yasunoxx/Z80proto/sch/Z80proto2/SPI40x4LCD.kicad_sch

## KiCad design sch/Z80proto2/SPI40x4LCD.kicad_sch (2025-04-16)

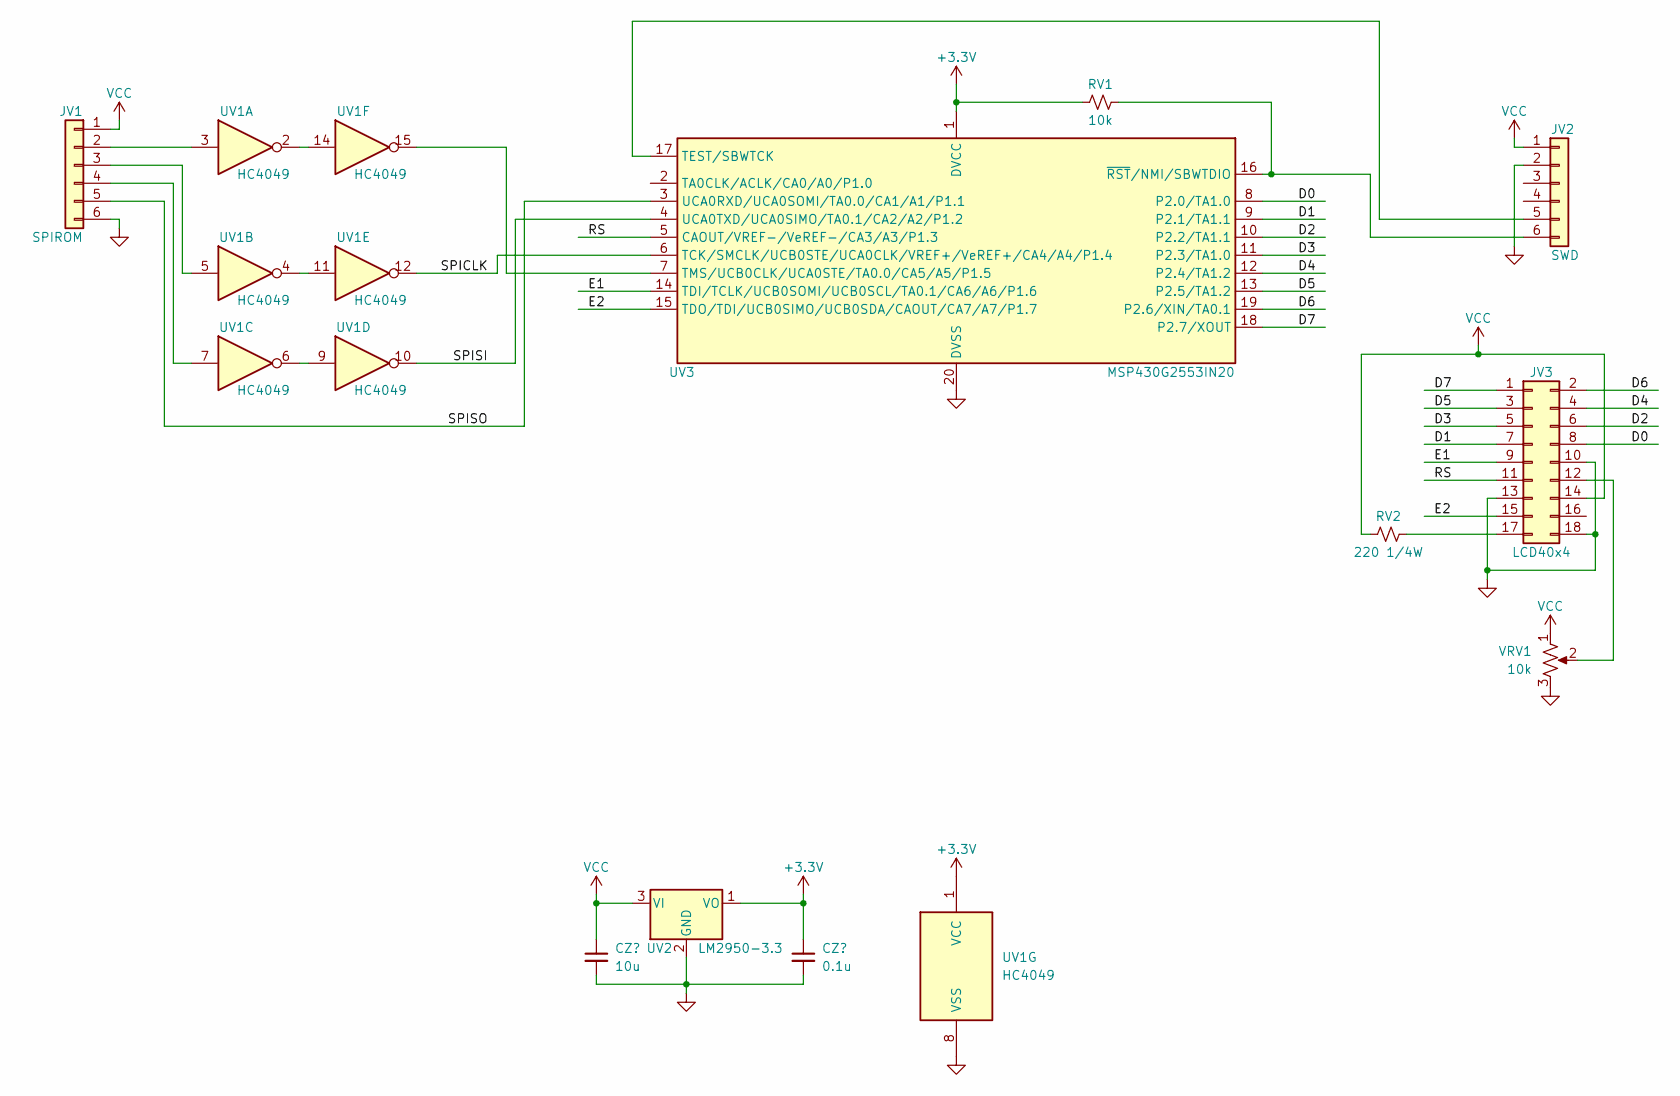
[picture p12: schematic SPI40x4LCD.kicad_sch]

Parts:
JV1: SPIROM
JV2: SWD
JV3: LCD40x4
RV1: 10k
RV2: 220 1/4W
UV1: HC4049
UV2: LM2950-3.3; TO-92_Inline
UV3: MSP430G2553IN20; DIP-20_W7.62mm
VRV1: 10k

Connections:
D0: JV3.8, UV3.8 (P2.0/TA1.0)
D1: JV3.7, UV3.9 (P2.1/TA1.1)
D2: JV3.6, UV3.10 (P2.2/TA1.1)
D3: JV3.5, UV3.11 (P2.3/TA1.0)
D4: JV3.4, UV3.12 (P2.4/TA1.2)
D5: JV3.3, UV3.13 (P2.5/TA1.2)
D6: JV3.2, UV3.19 (P2.6/XIN/TA0.1)
D7: JV3.1, UV3.18 (P2.7/XOUT)
E1: JV3.9, UV3.14 (TDI/TCLK/UCB0SOMI/UCB0SCL/TA0.1/CA6/A6/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)
E2: JV3.15, UV3.15 (TDO/TDI/UCB0SIMO/UCB0SDA/CAOUT/CA7/A7/P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)
unnamed: JV1.2, UV1.3
unnamed: JV1.3, UV1.5
unnamed: JV1.4, UV1.7
unnamed: JV2.5, UV3.17 (TEST/SBWTCK)
unnamed: JV2.6, RV1.2, UV3.16 (~RST/NMI/SBWTDIO)
unnamed: JV3.10, JV3.13, JV3.18
unnamed: JV3.12, VRV1.2
unnamed: JV3.14, RV2.1
unnamed: JV3.17, RV2.2
unnamed: RV1.1, UV3.1 (DVCC)
unnamed: UV1.6, UV1.9
unnamed: UV1.4, UV1.11
unnamed: UV1.2, UV1.14
unnamed: UV1.15, UV3.7 (TMS/UCB0CLK/UCA0STE/TA0.0/CA5/A5/P1.5)
RS: JV3.11, UV3.5 (CAOUT/VREF-/VeREF-/CA3/A3/P1.3)
SPICLK: UV1.12, UV3.6 (TCK/SMCLK/UCB0STE/UCA0CLK/VREF+/VeREF+/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)
SPISI: UV1.10, UV3.4 (UCA0TXD/UCA0SIMO/TA0.1/CA2/A2/P1.2)
SPISO: JV1.5, UV3.3 (UCA0RXD/UCA0SOMI/TA0.0/CA1/A1/P1.1)
