yasunoxx/Z80proto/sch/Z80proto-SAKI80/Comm_Module.kicad_sch

## KiCad design sch/Z80proto-SAKI80/Comm_Module.kicad_sch (2025-09-18, an earlier design)

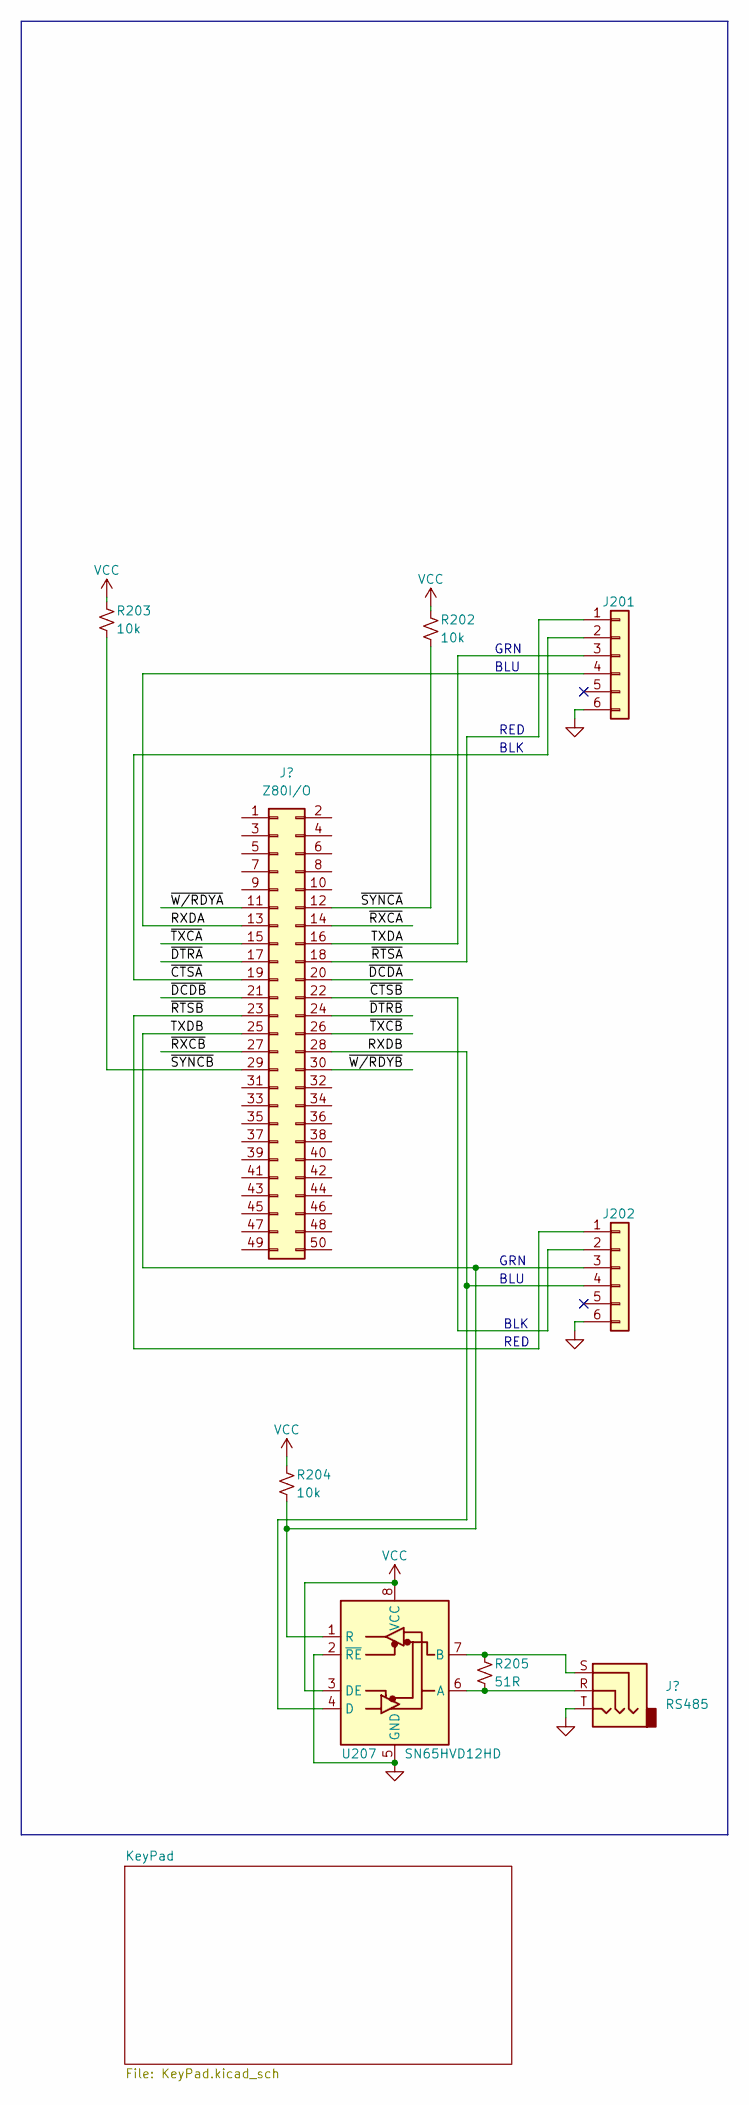
[picture p16: schematic Comm_Module.kicad_sch]

Parts:
J201, J202: Conn_01x06
R202, R203, R204: 10k
R205: 51R
U207: SN65HVD12HD; SOIC-8_3.9x4.9mm_P1.27mm

Connections:
unnamed: R205.1, U207.7 (B)
unnamed: R205.2, U207.6 (A)
unnamed: U207.2 (~RE), U207.5 (GND)
unnamed: U207.3 (DE), U207.8 (VCC)
RXDA: J201.4
RXDB: J202.4, U207.4 (D)
TXDA: J201.3
TXDB: J202.3, R204.2, U207.1 (R)
~CTSA: J201.2
~CTSB: J202.2
~RTSA: J201.1
~RTSB: J202.1
~SYNCA: R202.2
~SYNCB: R203.2

Notes on the sheet:
BLK
RED
BLU
GRN
