yasunoxx/Z80proto/sch/Z80proto-SAKI80/Z80proto-SAKI80.kicad_sch

## KiCad design sch/Z80proto-SAKI80/Z80proto-SAKI80.kicad_sch (2025-07-02, an earlier design)

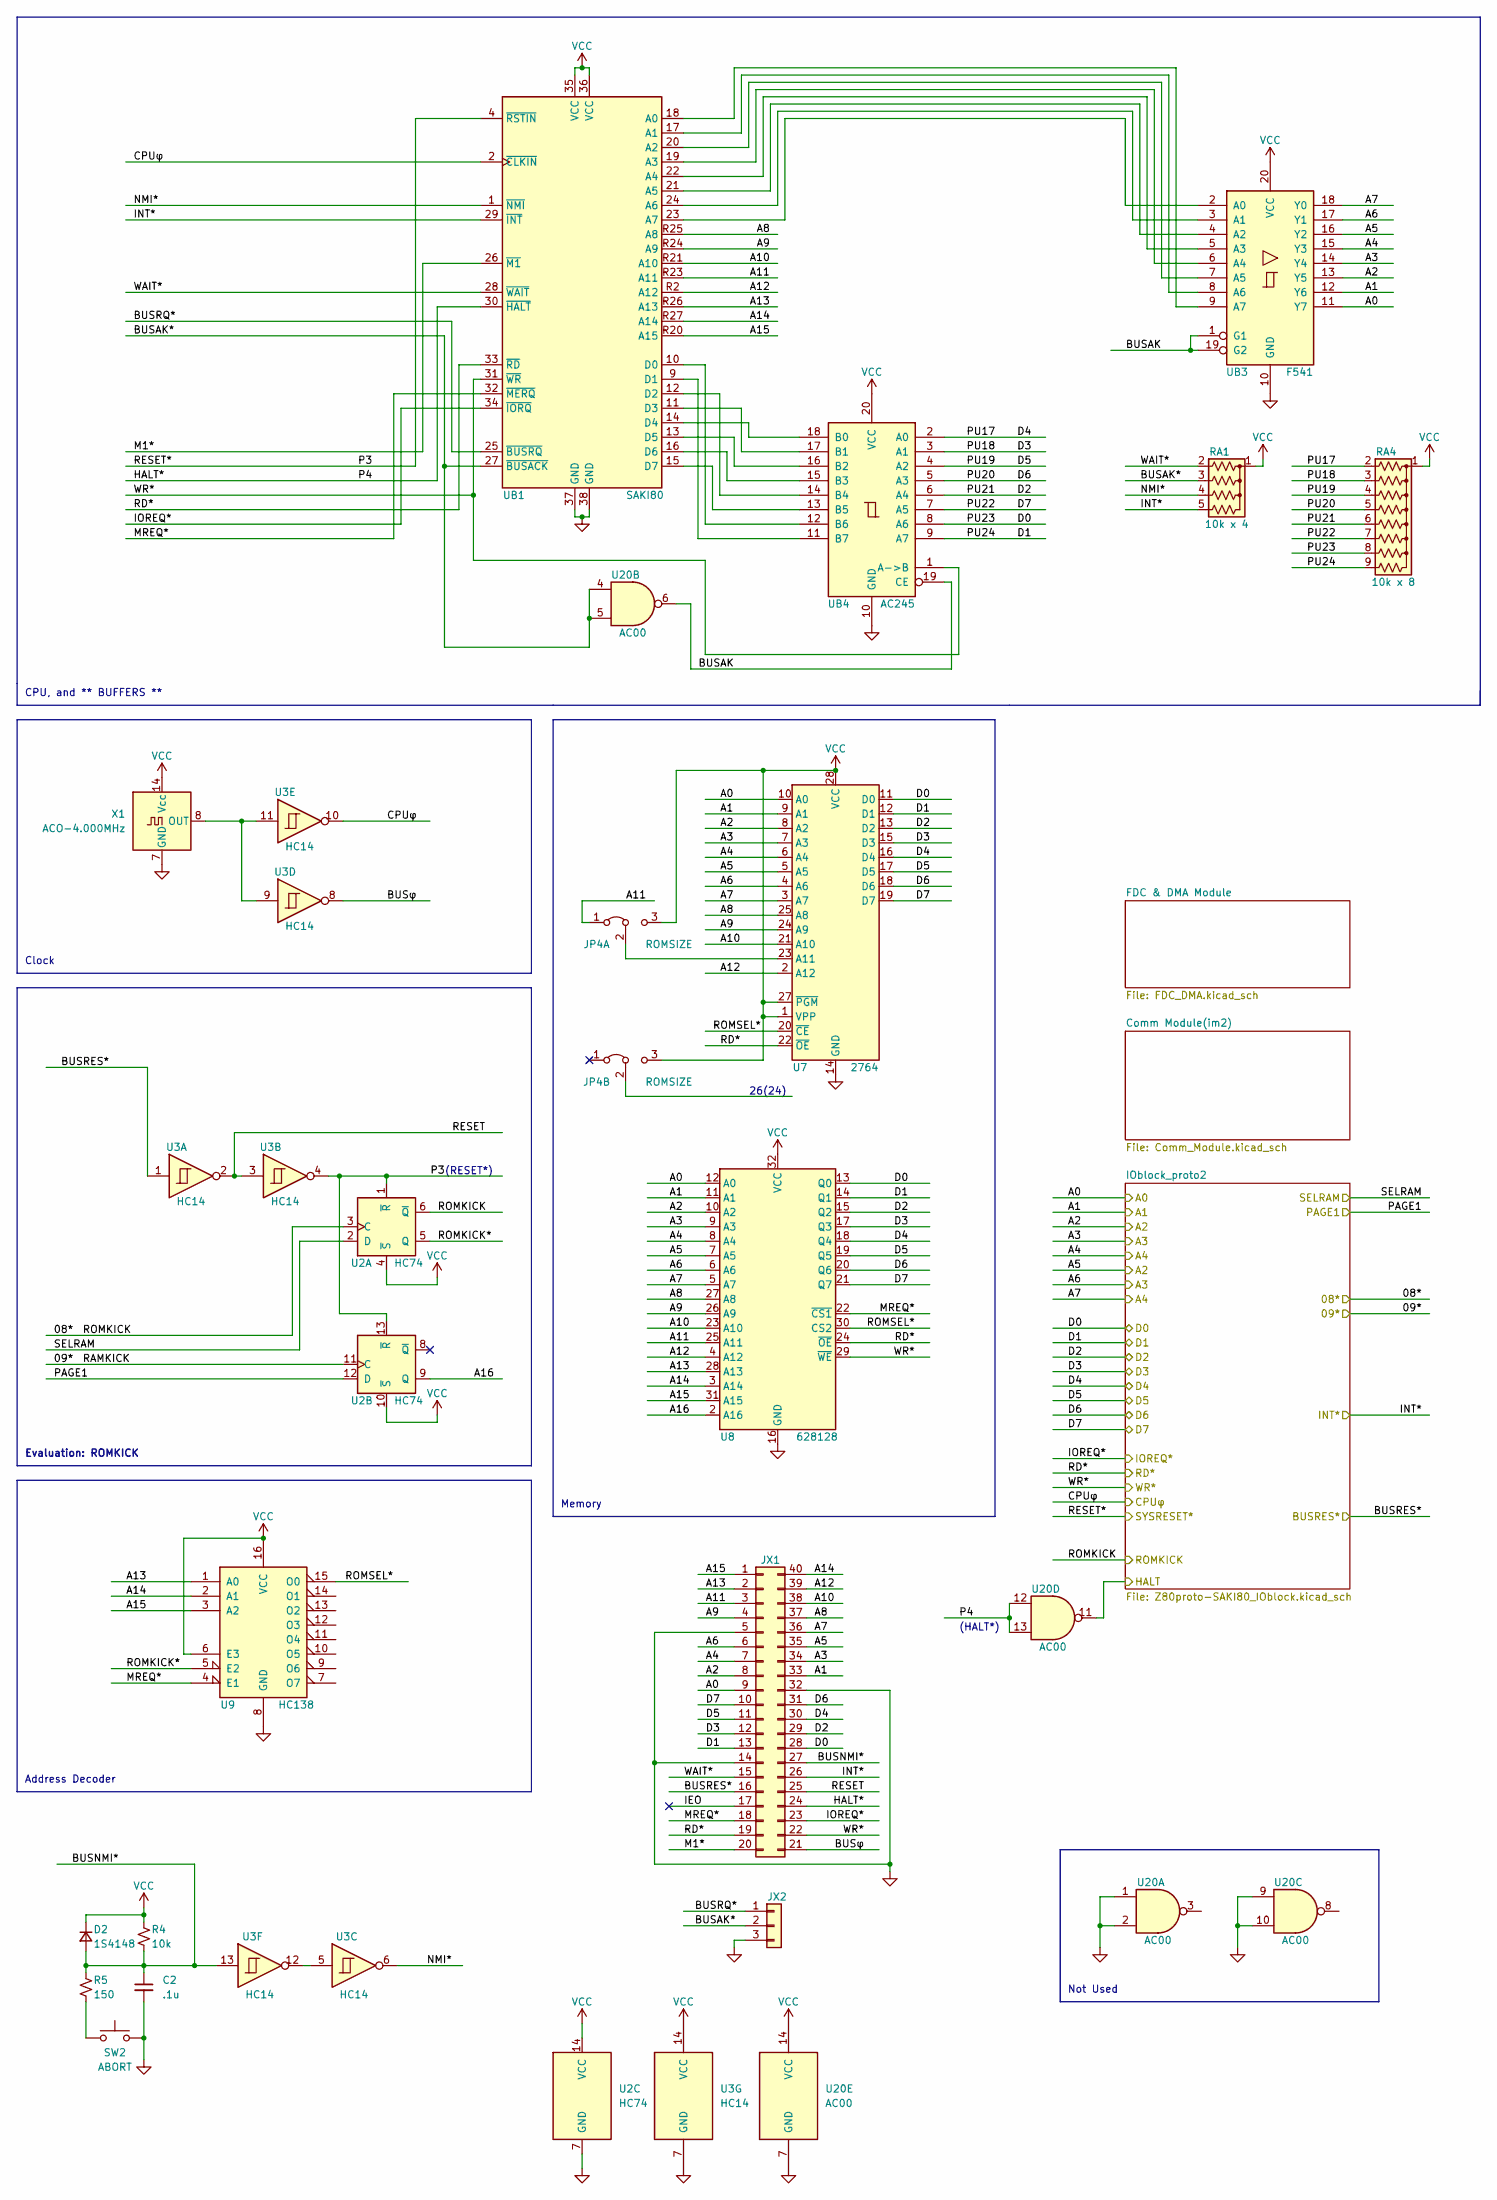
[picture p17: schematic Z80proto-SAKI80.kicad_sch]

Parts:
C2: .1u
D2: 1S4148
JP4A, JP4B: ROMSIZE
JX1: Conn_02x20_Counter_Clockwise
JX2: Conn_01x03
R4: 10k
R5: 150
RA1: 10k x 4; R_Array_SIP5
RA4: 10k x 8; R_Array_SIP9
SW2: ABORT
U2: HC74
U3: HC14
U7: 2764; DIP-28_W15.24mm
U8: 628128
U9: HC138
U20: AC00
UB1: SAKI80
UB3: F541
UB4: AC245
X1: ACO-4.000MHz; Oscillator_DIP-14

Connections:
08*: U2.3 (C), U2.6 (~Q)
09*: U2.11 (C)
A0: JX1.9, U7.10 (A0), U8.12 (A0), UB3.11 (Y7)
A1: JX1.33, U7.9 (A1), U8.11 (A1), UB3.12 (Y6)
A2: JX1.8, JX1.35, U7.5 (A5), U7.8 (A2), U8.7 (A5), U8.10 (A2), UB3.13 (Y5), UB3.16 (Y2)
A3: JX1.6, JX1.34, U7.4 (A6), U7.7 (A3), U8.6 (A6), U8.9 (A3), UB3.14 (Y4), UB3.17 (Y1)
A4: JX1.7, JX1.36, U7.3 (A7), U7.6 (A4), U8.5 (A7), U8.8 (A4), UB3.15 (Y3), UB3.18 (Y0)
A8: JX1.37, U7.25 (A8), U8.27 (A8), UB1.R25 (A8)
A9: JX1.4, U7.24 (A9), U8.26 (A9), UB1.R24 (A9)
A10: JX1.38, U7.21 (A10), U8.23 (A10), UB1.R21 (A10)
A11: JP4A.1 (A), JX1.3, U8.25 (A11), UB1.R23 (A11)
A12: JX1.39, U7.2 (A12), U8.4 (A12), UB1.R2 (A12)
A13: JX1.2, U8.28 (A13), U9.1 (A0), UB1.R26 (A13)
A14: JX1.40, U8.3 (A14), U9.2 (A1), UB1.R27 (A14)
A15: JX1.1, U8.31 (A15), U9.3 (A2), UB1.R20 (A15)
A16: U2.9 (Q), U8.2 (A16)
BUSAK: U20.6, UB3.1 (G1), UB3.19 (G2), UB4.19 (CE)
BUSAK*: JX2.2, RA1.3 (R2), U20.4, U20.5, UB1.27 (~BUSACK)
BUSNMI*: C2.1, D2.2 (A), JX1.27, R4.2, R5.1, U3.13
BUSRES*: JX1.16, U3.1
BUSRQ*: JX2.1, UB1.25 (~BUSRQ)
BUSφ: JX1.21, U3.8
CPUφ: U3.10, UB1.2 (~CLKIN)
D0: JX1.28, RA4.8 (R7), U7.11 (D0), U8.13 (Q0), UB4.8 (A6)
D1: JX1.13, RA4.9 (R8), U7.12 (D1), U8.14 (Q1), UB4.9 (A7)
D2: JX1.29, RA4.6 (R5), U7.13 (D2), U8.15 (Q2), UB4.6 (A4)
D3: JX1.12, RA4.3 (R2), U7.15 (D3), U8.17 (Q3), UB4.3 (A1)
D4: JX1.30, RA4.2 (R1), U7.16 (D4), U8.18 (Q4), UB4.2 (A0)
D5: JX1.11, RA4.4 (R3), U7.17 (D5), U8.19 (Q5), UB4.4 (A2)
D6: JX1.31, RA4.5 (R4), U7.18 (D6), U8.20 (Q6), UB4.5 (A3)
D7: JX1.10, RA4.7 (R6), U7.19 (D7), U8.21 (Q7), UB4.7 (A5)
HALT: U20.11
HALT*: JX1.24, U20.12, U20.13, UB1.30 (~HALT)
IEO: JX1.17
INT*: JX1.26, RA1.5 (R4), UB1.29 (~INT)
IOREQ*: JX1.23, UB1.34 (~IORQ)
M1*: JX1.20, UB1.26 (~M1)
MREQ*: JX1.18, U8.22 (~CS1), U9.4 (E1), UB1.32 (~MERQ)
NMI*: RA1.4 (R3), U3.6, UB1.1 (~NMI)
unnamed: C2.2, SW2.2
unnamed: D2.1 (K), R4.1
unnamed: JP4A.2 (C), U7.23 (A11)
unnamed: JP4A.3 (B), JP4B.3 (B), U7.1 (VPP), U7.27 (~PGM), U7.28 (VCC)
unnamed: JX1.5, JX1.14, JX1.32
unnamed: R5.2, SW2.1
unnamed: U3.9, U3.11, X1.8 (OUT)
unnamed: U3.5, U3.12
unnamed: U9.6 (E3), U9.16 (VCC)
unnamed: U20.1, U20.2
unnamed: U20.9, U20.10
unnamed: UB1.9 (D1), UB4.11 (B7)
unnamed: UB1.10 (D0), UB4.12 (B6)
unnamed: UB1.11 (D3), UB4.17 (B1)
unnamed: UB1.12 (D2), UB4.14 (B4)
unnamed: UB1.13 (D5), UB4.16 (B2)
unnamed: UB1.14 (D4), UB4.18 (B0)
unnamed: UB1.15 (D7), UB4.13 (B5)
unnamed: UB1.16 (D6), UB4.15 (B3)
unnamed: UB1.17 (A1), UB3.8 (A6)
unnamed: UB1.18 (A0), UB3.9 (A7)
unnamed: UB1.19 (A3), UB3.6 (A4)
unnamed: UB1.20 (A2), UB3.7 (A5)
unnamed: UB1.21 (A5), UB3.4 (A2)
unnamed: UB1.22 (A4), UB3.5 (A3)
unnamed: UB1.23 (A7), UB3.2 (A0)
unnamed: UB1.24 (A6), UB3.3 (A1)
unnamed: UB1.35 (VCC), UB1.36 (VCC)
unnamed: UB1.37 (GND), UB1.38 (GND)
P3: U2.1 (~R), U2.13 (~R), U3.4, UB1.4 (~RSTIN)
PAGE1: U2.12 (D)
RD*: JX1.19, U7.22 (~OE), U8.24 (~OE), UB1.33 (~RD)
RESET: JX1.25, U3.2, U3.3
ROMKICK*: U2.5 (Q), U9.5 (E2)
ROMSEL*: U7.20 (~CE), U8.30 (CS2), U9.15 (O0)
SELRAM: U2.2 (D)
WAIT*: JX1.15, RA1.2 (R1), UB1.28 (~WAIT)
WR*: JX1.22, U8.29 (~WE), UB1.31 (~WR), UB4.1 (A->B)

Notes on the sheet:
(RESET*)
Evaluation: ROMKICK
(HALT*)
Memory
CPU, and ** BUFFERS **
Address Decoder
Not Used
26(24)
Clock
