yasunoxx/Z80proto/sch/Z80proto-SAKI80/Z80proto-SAKI80_AFIFO.kicad_sch

## KiCad design sch/Z80proto-SAKI80/Z80proto-SAKI80_AFIFO.kicad_sch (2025-07-02)

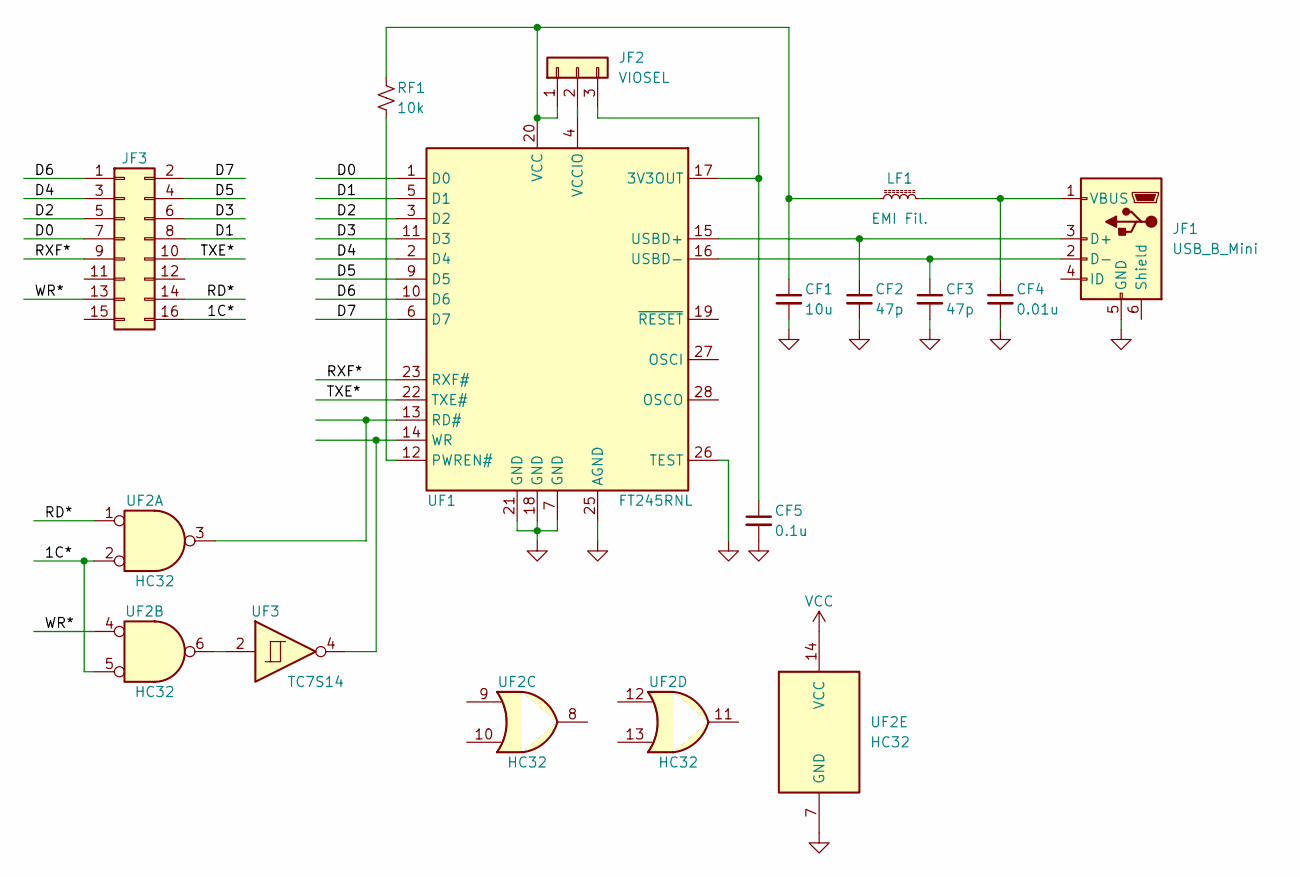
[picture p18: schematic Z80proto-SAKI80_AFIFO.kicad_sch]

Parts:
CF1: 10u
CF2, CF3: 47p
CF4: 0.01u
CF5: 0.1u
JF1: USB_B_Mini
JF2: VIOSEL
JF3: Conn_02x08_Odd_Even
LF1: EMI Fil.
RF1: 10k
UF1: FT245RNL
UF2: HC32
UF3: TC7S14

Connections:
1C*: JF3.16, UF2.2, UF2.5
D0: JF3.7, UF1.1 (D0)
D1: JF3.8, UF1.5 (D1)
D2: JF3.5, UF1.3 (D2)
D3: JF3.6, UF1.11 (D3)
D4: JF3.3, UF1.2 (D4)
D5: JF3.4, UF1.9 (D5)
D6: JF3.1, UF1.10 (D6)
D7: JF3.2, UF1.6 (D7)
unnamed: CF1.1, JF2.1, LF1.1, RF1.1, UF1.20 (VCC)
unnamed: CF2.1, JF1.3 (D+), UF1.15 (USBD+)
unnamed: CF3.1, JF1.2 (D-), UF1.16 (USBD-)
unnamed: CF4.1, JF1.1 (VBUS), LF1.2
unnamed: CF5.1, JF2.3, UF1.17 (3V3OUT)
unnamed: JF2.2, UF1.4 (VCCIO)
unnamed: RF1.2, UF1.12 (PWREN#)
unnamed: UF1.13 (RD#), UF2.3
unnamed: UF1.14 (WR), UF3.4
unnamed: UF1.7 (GND), UF1.18 (GND), UF1.21 (GND)
unnamed: UF2.6, UF3.2
RD*: JF3.14, UF2.1
RXF*: JF3.9, UF1.23 (RXF#)
TXE*: JF3.10, UF1.22 (TXE#)
WR*: JF3.13, UF2.4
