yasunoxx/Z80proto/sch/Z80proto-SAKI80/Z80proto_IOblock_7seg.kicad_sch

## KiCad design sch/Z80proto-SAKI80/Z80proto_IOblock_7seg.kicad_sch (2025-07-02)

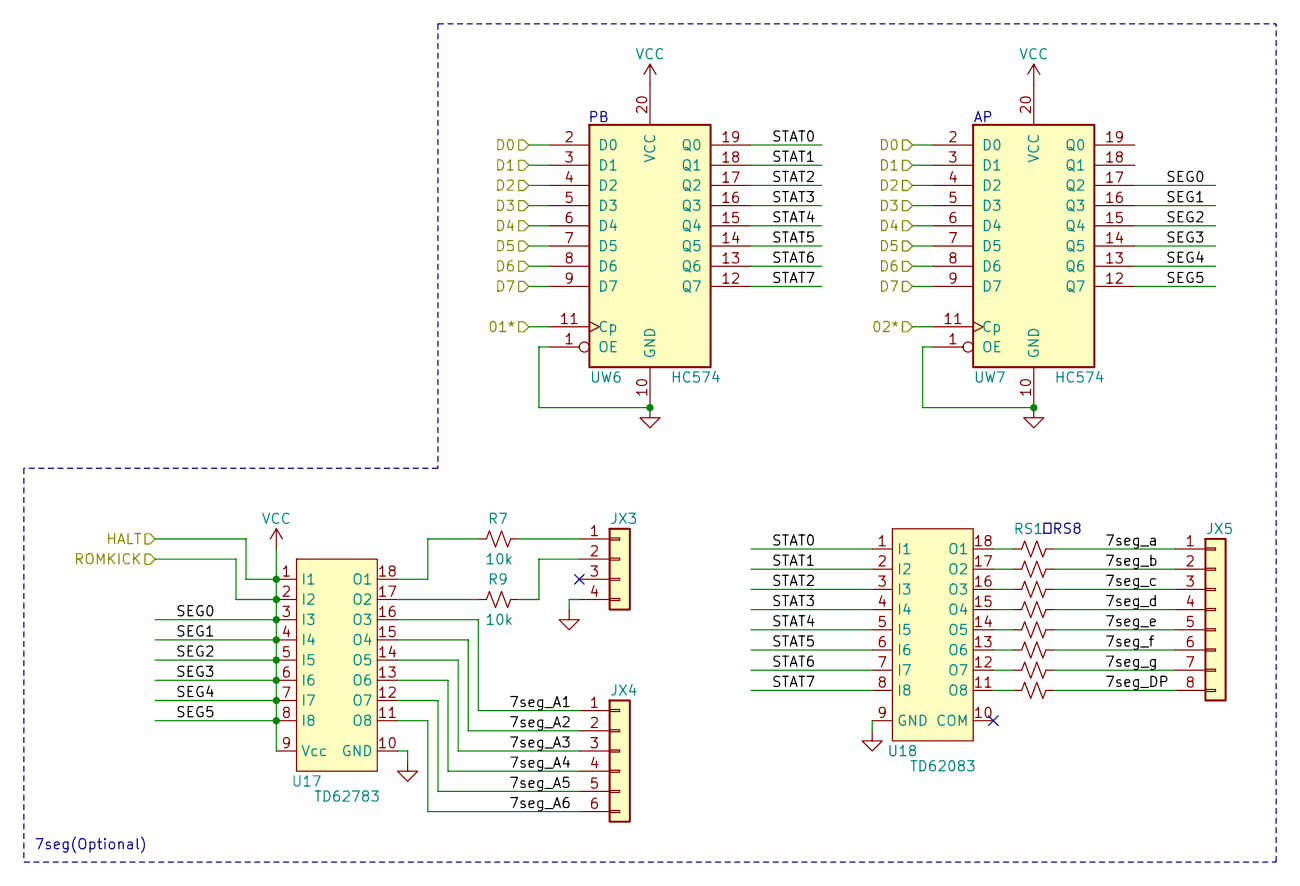
[picture p20: schematic Z80proto_IOblock_7seg.kicad_sch]

Parts:
JX3: Conn_01x04
JX4: Conn_01x06
JX5: Conn_01x08
R7, R9: 10k
RS1: 1k
U17: TD62783
U18: TD62083
UW6, UW7: HC574

Connections:
01*: UW6.11 (Cp)
02*: UW7.11 (Cp)
7seg_A1: JX4.1, U17.16 (O3)
7seg_A2: JX4.2, U17.15 (O4)
7seg_A3: JX4.3, U17.14 (O5)
7seg_A4: JX4.4, U17.13 (O6)
7seg_A5: JX4.5, U17.12 (O7)
7seg_A6: JX4.6, U17.11 (O8)
7seg_DP: JX5.8
7seg_a: JX5.1, RS1.2
7seg_b: JX5.2
7seg_c: JX5.3
7seg_d: JX5.4
7seg_e: JX5.5
7seg_f: JX5.6
7seg_g: JX5.7
D0: UW6.2 (D0), UW7.2 (D0)
D1: UW6.3 (D1), UW7.3 (D1)
D2: UW6.4 (D2), UW7.4 (D2)
D3: UW6.5 (D3), UW7.5 (D3)
D4: UW6.6 (D4), UW7.6 (D4)
D5: UW6.7 (D5), UW7.7 (D5)
D6: UW6.8 (D6), UW7.8 (D6)
D7: UW6.9 (D7), UW7.9 (D7)
HALT: U17.1 (I1), U17.2 (I2), U17.3 (I3), U17.4 (I4), U17.5 (I5), U17.6 (I6), U17.7 (I7), U17.8 (I8), U17.9 (Vcc), UW7.12 (Q7), UW7.13 (Q6), UW7.14 (Q5), UW7.15 (Q4), UW7.16 (Q3), UW7.17 (Q2)
unnamed: JX3.1, R7.2
unnamed: JX3.2, R9.2
unnamed: R7.1, U17.18 (O1)
unnamed: R9.1, U17.17 (O2)
unnamed: RS1.1, U18.18 (O1)
unnamed: UW6.1 (OE), UW6.10 (GND)
unnamed: UW7.1 (OE), UW7.10 (GND)
STAT0: U18.1 (I1), UW6.19 (Q0)
STAT1: U18.2 (I2), UW6.18 (Q1)
STAT2: U18.3 (I3), UW6.17 (Q2)
STAT3: U18.4 (I4), UW6.16 (Q3)
STAT4: U18.5 (I5), UW6.15 (Q4)
STAT5: U18.6 (I6), UW6.14 (Q5)
STAT6: U18.7 (I7), UW6.13 (Q6)
STAT7: U18.8 (I8), UW6.12 (Q7)

Notes on the sheet:
～RS8
7seg(Optional)
