yasunoxx/Z80proto/sch/FDC/FDC/FDC.kicad_sch

## KiCad design sch/FDC/FDC/FDC.kicad_sch (2025-04-16)

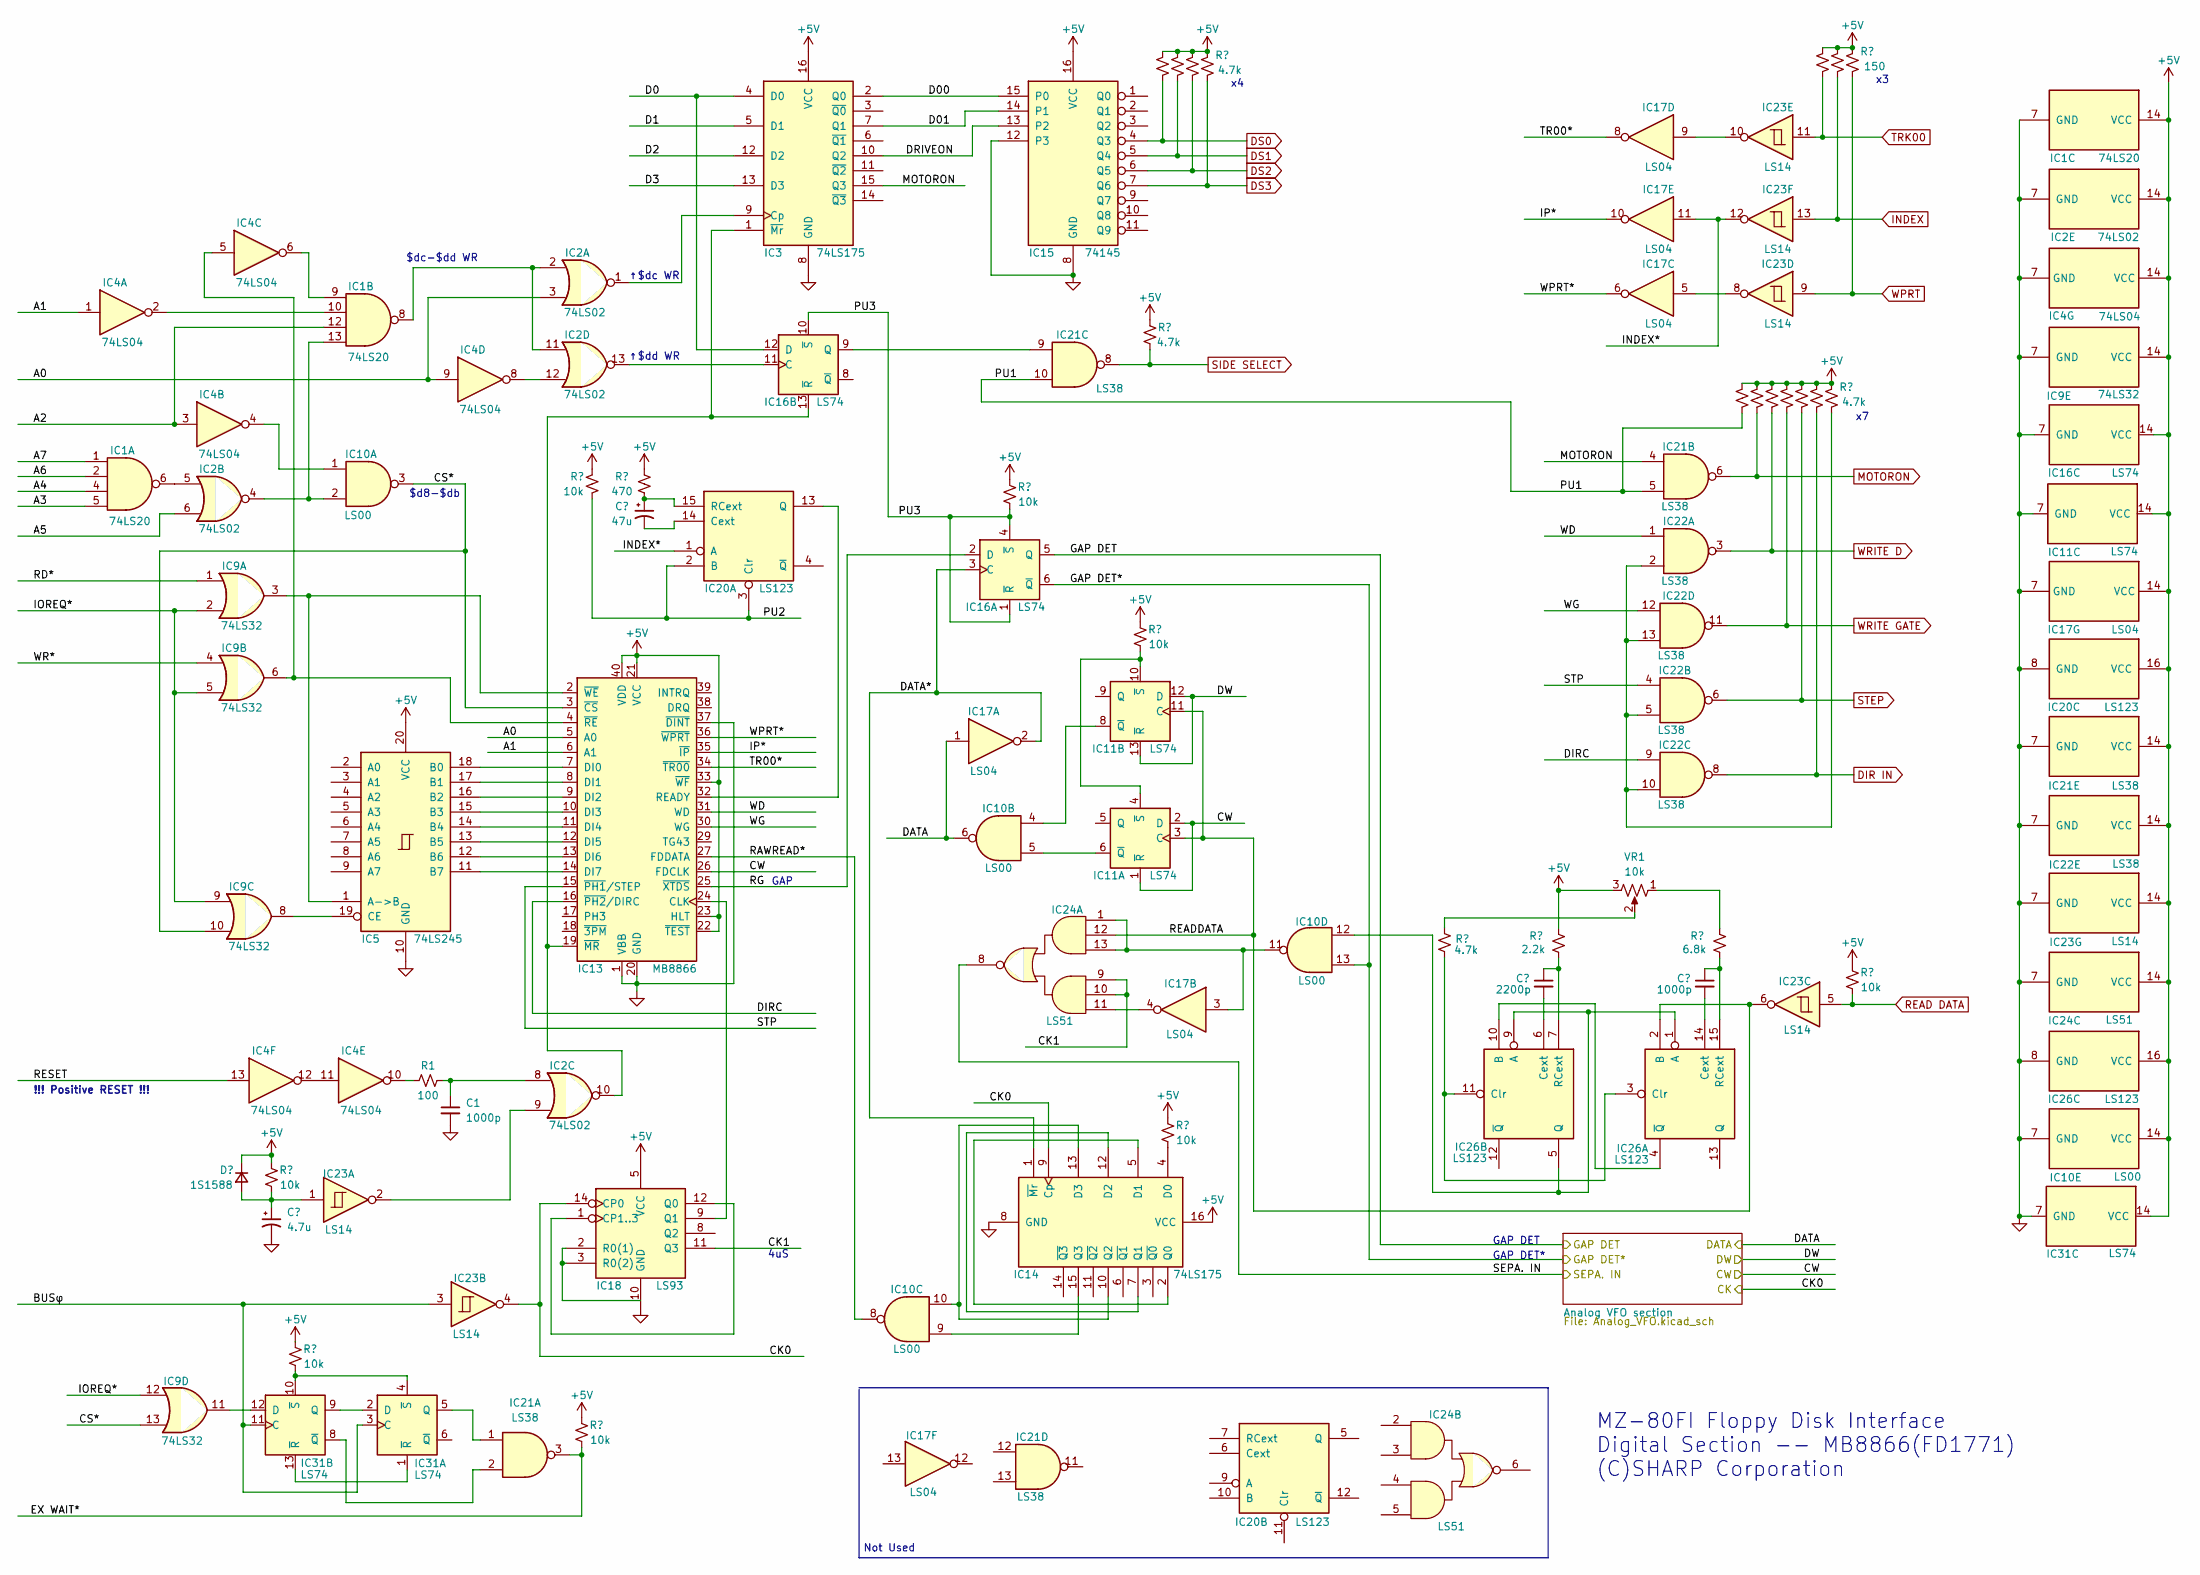
[picture p21: schematic FDC.kicad_sch]

Parts:
C1: 1000p
IC1: 74LS20
IC2: 74LS02
IC3, IC14: 74LS175
IC4: 74LS04
IC5: 74LS245
IC9: 74LS32
IC10: LS00
IC11, IC16, IC31: LS74
IC13: MB8866; DIP-40_W15.24mm
IC15: 74145
IC17: LS04
IC18: LS93
IC20, IC26: LS123
IC21, IC22: LS38
IC23: LS14
IC24: LS51
R1: 100
VR1: 10k

Connections:
A0: IC2.3, IC4.9, IC13.5 (A0)
A1: IC4.1, IC13.6 (A1)
A2: IC1.12, IC4.3
A3: IC1.5
A4: IC1.4
A5: IC2.6
A6: IC1.2
A7: IC1.1
BUSφ: IC23.3, IC31.3 (C), IC31.11 (C)
CK: IC14.9 (Cp), IC18.14 (CP0), IC23.4
CK1: IC18.11 (Q3), IC24.9, IC24.10
CS*: IC9.10, IC9.13, IC10.3, IC13.3 (~CS)
CW: IC11.1 (~R), IC11.2 (D), IC13.26 (FDCLK)
D00: IC3.2 (Q0), IC15.15 (P0)
D0: IC3.4 (D0), IC16.12 (D)
D01: IC3.7 (Q1), IC15.14 (P1)
D1: IC3.5 (D1)
D2: IC3.12 (D2)
D3: IC3.13 (D3)
DATA: IC10.6, IC17.1
DATA*: IC14.1 (~Mr), IC16.3 (C), IC17.2
DIR IN: IC22.8
DIRC: IC13.16 (~PH2/DIRC), IC22.9
DRIVEON: IC3.10 (Q2), IC15.13 (P2)
DS0: IC15.4 (Q3)
DS1: IC15.5 (Q4)
DS2: IC15.6 (Q5)
DS3: IC15.7 (Q6)
DW: IC11.12 (D), IC11.13 (~R)
EX WAIT*: IC21.3
GAP DET: IC16.5 (Q)
GAP DET*: IC10.13, IC16.6 (~Q)
INDEX: IC23.13
INDEX*: IC17.11, IC20.1 (A), IC23.12
IOREQ*: IC9.2, IC9.5, IC9.9, IC9.12
IP*: IC13.35 (~IP), IC17.10
MOTORON: IC3.15 (Q3), IC21.4, IC21.6
unnamed: C1.1, IC2.8, R1.2
unnamed: IC1.6, IC2.5
unnamed: IC1.7 (GND), IC2.7 (GND), IC4.7 (GND), IC9.7 (GND), IC10.7 (GND), IC11.7 (GND), IC16.7 (GND), IC17.7 (GND), IC20.8 (GND), IC21.7 (GND), IC22.7 (GND), IC23.7 (GND), IC24.7 (GND), IC26.8 (GND), IC31.7 (GND)
unnamed: IC1.8, IC2.2, IC2.11
unnamed: IC1.9, IC4.6
unnamed: IC1.10, IC4.2
unnamed: IC1.13, IC2.4, IC10.2
unnamed: IC1.14 (VCC), IC2.14 (VCC), IC4.14 (VCC), IC9.14 (VCC), IC10.14 (VCC), IC11.14 (VCC), IC16.14 (VCC), IC17.14 (VCC), IC20.16 (VCC), IC21.14 (VCC), IC22.14 (VCC), IC23.14 (VCC), IC24.14 (VCC), IC26.16 (VCC), IC31.14 (VCC)
unnamed: IC2.1, IC3.9 (Cp)
unnamed: IC2.9, IC23.2
unnamed: IC2.12, IC4.8
unnamed: IC4.10, R1.1
unnamed: IC4.11, IC4.12
unnamed: IC5.19 (CE), IC9.8
unnamed: IC4.4, IC10.1
unnamed: IC10.4, IC11.8 (~Q)
unnamed: IC10.5, IC11.6 (~Q)
unnamed: IC10.9, IC14.15 (Q3)
unnamed: IC10.10, IC14.10 (Q2), IC14.13 (D3)
unnamed: IC10.11, IC17.3, IC24.1, IC24.13
unnamed: IC10.12, IC26.1 (A), IC26.5 (Q), IC26.9 (A)
unnamed: IC11.4 (~S), IC11.10 (~S)
unnamed: IC13.1 (VBB), IC13.20 (GND), IC13.37 (~DINT)
unnamed: IC5.1 (A->B), IC9.3, IC13.2 (~WE)
unnamed: IC4.5, IC9.6, IC13.4 (~RE)
unnamed: IC5.18 (B0), IC13.7 (DI0)
unnamed: IC5.17 (B1), IC13.8 (DI1)
unnamed: IC5.16 (B2), IC13.9 (DI2)
unnamed: IC5.15 (B3), IC13.10 (DI3)
unnamed: IC5.14 (B4), IC13.11 (DI4)
unnamed: IC5.13 (B5), IC13.12 (DI5)
unnamed: IC5.12 (B6), IC13.13 (DI6)
unnamed: IC5.11 (B7), IC13.14 (DI7)
unnamed: IC2.10, IC3.1 (~Mr), IC13.19 (~MR), IC16.13 (~R)
unnamed: IC13.21 (VCC), IC13.22 (~TEST), IC13.23 (HLT), IC13.33 (~WF), IC13.40 (VDD)
unnamed: IC13.24 (CLK), IC18.9 (Q1)
unnamed: IC13.32 (READY), IC20.13 (Q)
unnamed: IC14.2 (Q0), IC14.5 (D1)
unnamed: IC14.7 (Q1), IC14.12 (D2)
unnamed: IC15.8 (GND), IC15.12 (P3)
unnamed: IC16.9 (Q), IC21.9
unnamed: IC2.13, IC16.11 (C)
unnamed: IC17.4, IC24.11
unnamed: IC17.5, IC23.8
unnamed: IC17.9, IC23.10
unnamed: IC18.1 (CP1..3), IC18.12 (Q0)
unnamed: IC18.2 (R0(1)), IC18.3 (R0(2))
unnamed: IC21.1, IC31.5 (Q)
unnamed: IC21.2, IC31.8 (~Q)
unnamed: IC22.2, IC22.5, IC22.10, IC22.13
unnamed: IC26.4 (~Q), IC26.10 (B)
unnamed: IC26.3 (Clr), IC26.11 (Clr)
unnamed: IC31.1 (~R), IC31.13 (~R)
unnamed: IC31.2 (D), IC31.9 (Q)
unnamed: IC31.4 (~S), IC31.10 (~S)
unnamed: IC9.11, IC31.12 (D)
PU1: IC21.5, IC21.10
PU2: IC20.2 (B), IC20.3 (Clr)
PU3: IC16.1 (~R), IC16.4 (~S), IC16.10 (~S)
RAWREAD*: IC10.8, IC13.27 (FDDATA)
RD*: IC9.1
READ DATA: IC23.5
READDATA: IC11.3 (C), IC11.11 (C), IC23.6, IC24.12, IC26.2 (B)
RESET: IC4.13
RG: IC13.25 (~XTDS), IC16.2 (D)
SEPA. IN: IC24.8
SIDE SELECT: IC21.8
STEP: IC22.6
STP: IC13.15 (~PH1/STEP), IC22.4
TR00*: IC13.34 (~TR00), IC17.8
TRK00: IC23.11
WD: IC13.31 (WD), IC22.1
WG: IC13.30 (WG), IC22.12
WPRT: IC23.9
WPRT*: IC13.36 (~WPRT), IC17.6
WR*: IC9.4
WRITE D: IC22.3
WRITE GATE: IC22.11

Notes on the sheet:
GAP DET*
$dc-$dd WR
GAP
MZ-80FI Floppy Disk Interface Digital Section -- MB8866(FD1771) (C)SHARP Corporation
Not Used
↑$dd WR
$d8-$db
GAP DET
4uS
↑$dc WR
!!! Positive RESET !!!
