yasunoxx/Z80proto/srcs/MiniMon/tmhost/control.h

// control.h -- ASCII contrrol characters

#ifndef _CONTROL_H_
#define _CONTROL_H_

#define NUL 0
#define SOH 1
#define STX 2
#define ETX 3
#define EOT 4
#define ENQ 5
#define ACK 6
#define NAK 0x15
#define SYN 0x16
#define CAN 0x18
#define CHR_C   0x43
#define SPC 32
#define CPMEOF  28

#define PAD 0x0FF // dummy

#define CR  13
#define LF  11
#define ESC 27
#define DEL 127

#endif // _CONTROL_H_
