yasunoxx/Z80proto/srcs/MiniMon-C/config.asm

;   config.asm - configuration for m_loader.asm

    DEFC RUN_ON_ROM = 0
    DEFC RUN_ON_RAM = 1
;;  !CHOOSE ANY ONE!: "run on ROM" or "run on RAM"
;    DEFC RUN_MODE = RUN_ON_ROM
    DEFC RUN_MODE = RUN_ON_RAM
;
;

;;  !CHOOSE ANY ONE!: interrupt mode IM2 or IM1
;  use im2
    DEFC INTERRUPT_MODE = 2
    im  2
;  use im1
;   DEFC INTERRUPT_MODE = 1
;    im  1

;;  !!!EDIT CAREFULLY!!!
    ld  sp, 0FFFFh


;   end config.asm
