yasunoxx/Z80proto/srcs/MiniMon/tmhost/parse.h

// parse.h -- header file for parse.h

#ifndef _PARSE_H_
#define _PARSE_H_
#include <stdbool.h>

typedef struct disRx
{
    uint8_t stx;            // +1
    uint8_t frameid[ 2 ];       // +2 = 3

    uint8_t syn;            // +1 = 4( +1 )
    uint8_t cmd[ 3 ];       // +3 = 7( +3 = 4 )
    uint8_t length;         // +1 = 8( +1 = 5 )
    uint8_t result[ 3 ];    // +3 = 11( +3 = 8 )
    // if( cmd[1] != 'M' ) pad + pad + result; else address + result;
    uint8_t rxarray[ 64 ];  // +64 = 75( +64 = 70 )

    uint8_t crc[ 2 ];           // +2 = 77
    uint8_t etx;            // +1 = 78
} _disRx;

extern const uint8_t RxFormat[ 13 ][ 10 ];
#ifdef _TMHOST_
extern const uint8_t TxFormat[ 13 ][ 80 ];
extern bool Check_RxBuffer( uint8_t * );
extern uint8_t ParseTxBuf( uint8_t );
#endif
#define IDX_STX 0
#define IDX_SEQH 1
#define IDX_SEQL 2
#define IDX_SYN 3
#define IDX_CMD0 4
#define IDX_CMD1 5
#define IDX_CMD2 6
#define IDX_SIZE 7
#define IDX_ADDRH 8
#define IDX_ADDRL 9
#define IDX_ACKNAK 10

// MAGIC NUMBER: FIFO_TRAILER_SIZE = 72, as BODY 72bytes
#define FIFO_TRAILER_SIZE 72
// MAGIC NUMBER: FIFO_PACKET_SIZE = 78, HEAD 3bytes + BODY 72bytes + TAIL 3bytes
#define FIFO_PACKET_SIZE 78

#define IDX_CRCH    FIFO_PACKET_SIZE - 3
#define IDX_CRCL    FIFO_PACKET_SIZE - 2
#define IDX_ETX     FIFO_PACKET_SIZE - 1

#define START   0   // Start Linkup
#define NOP     1   // No Operation/Keep Alive
#define SET_BP  2   // Set Breakpoint
#define REG     3   // Register Previous Breakpoint
#define WM64    4   // Write Memory 64bytes
#define RM64    5   // Read Memory 64bytes
#define WM01    6   // Write Memory 1 byte
#define RM01    7   // Read Memory 1 byte
#define INP     8   // Inport
#define OUTP    9   // Outport
#define TRACE   10  // Run with Trace
#define STOP    11  // Stop Run & Trace
#define QUIT    12  // Quit testmode

#endif // _PARSE_H_
